mbflv/Esp32-Relay-Aht10-Room_Thermostat/Pictures/aht10.jpeg

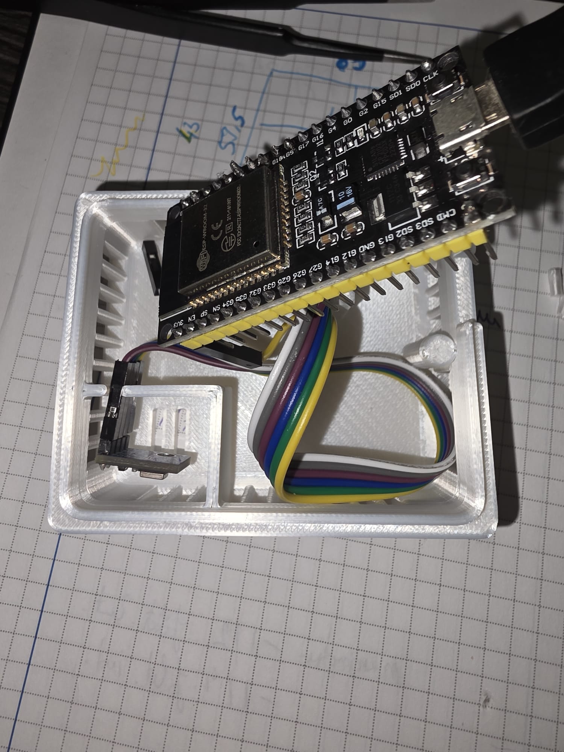
Pictures/aht10.jpeg
