mbflv/Esp32-Relay-Aht10-Room_Thermostat/Pictures/control.png

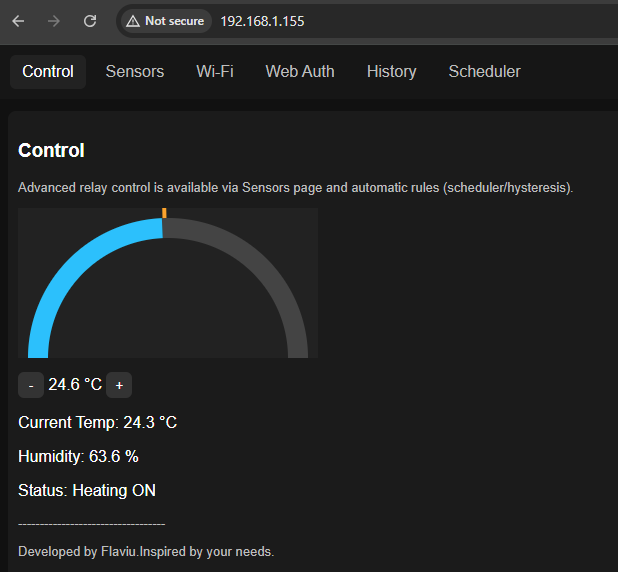
Pictures/control.png
