mbflv/Esp32-Relay-Aht10-Room_Thermostat/Pictures/schedule.png

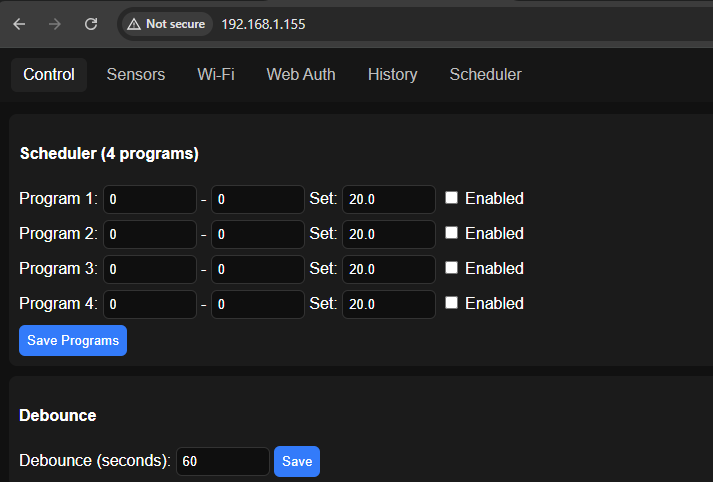
Pictures/schedule.png
