mbflv/Esp32-Relay-Aht10-Room_Thermostat/Pictures/sensor aht10.png

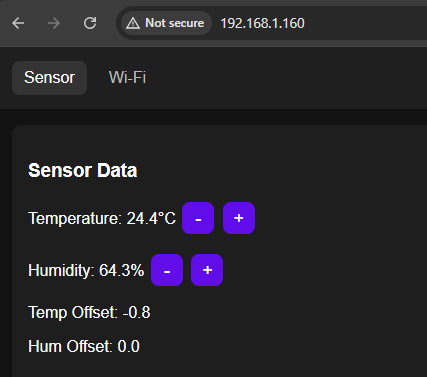
Pictures/sensor aht10.png
