mbflv/Esp32-Relay-Aht10-Room_Thermostat/Pictures/sensor.png

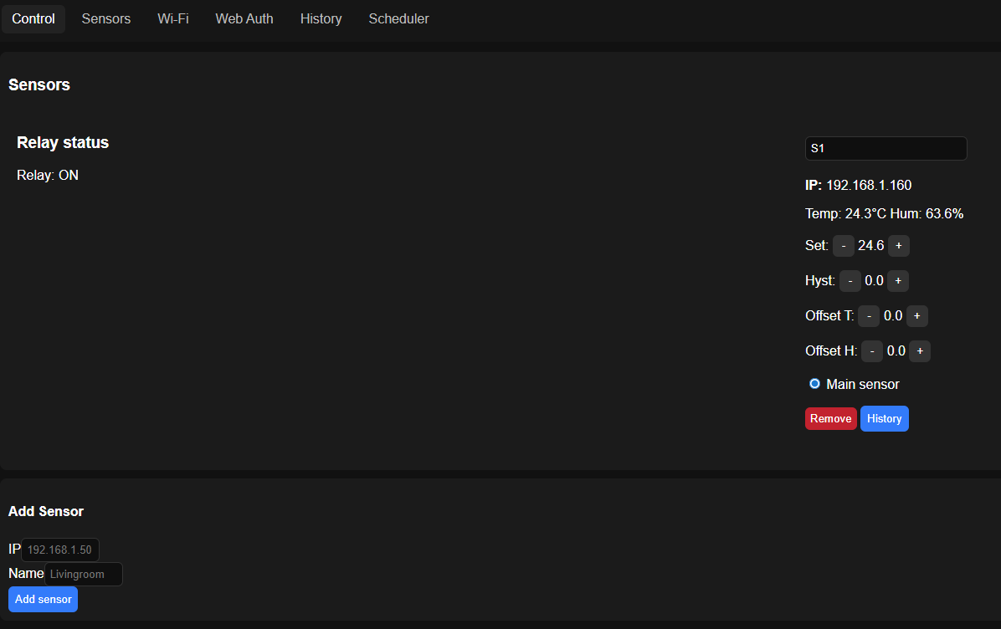
Pictures/sensor.png
