mbflv/Esp32-Relay-Aht10-Room_Thermostat/Pictures/history.png

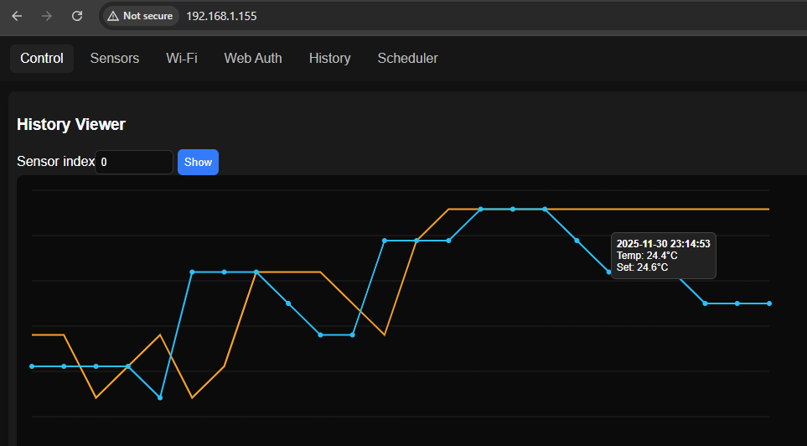
Pictures/history.png
